JJC86/MIG23MLD-Joystick-Gimbal/images/20210718_0329.png

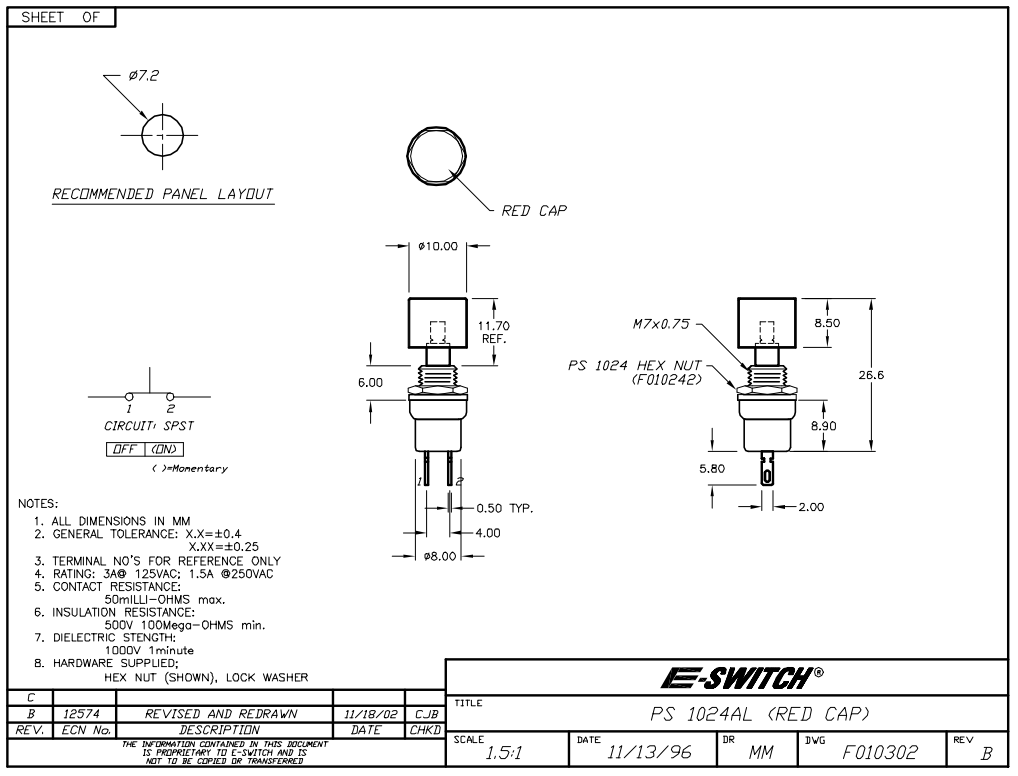
images/20210718_0329.png
