JJC86/MIG23MLD-Joystick-Gimbal/images/20210720_0145.png

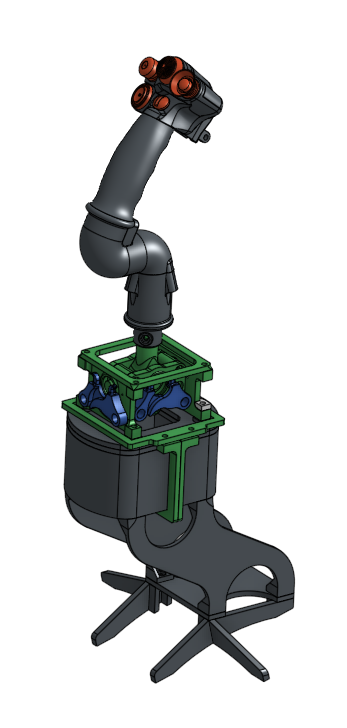
images/20210720_0145.png
