JJC86/MIG23MLD-Joystick-Gimbal/images/Image 001.png

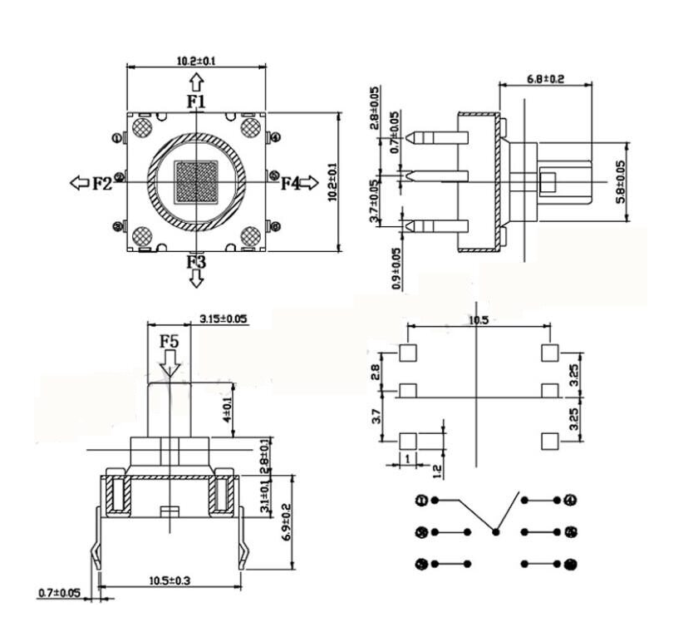
images/Image 001.png
