JJC86/MIG23MLD-Joystick-Gimbal/images/Image 002.png

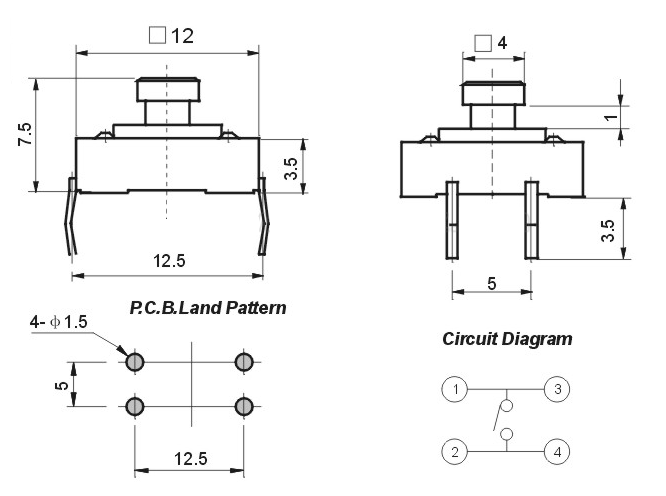
images/Image 002.png
